skaman82/PowerPuck/PCB Files/Final Gerber/square Rev22_b.png

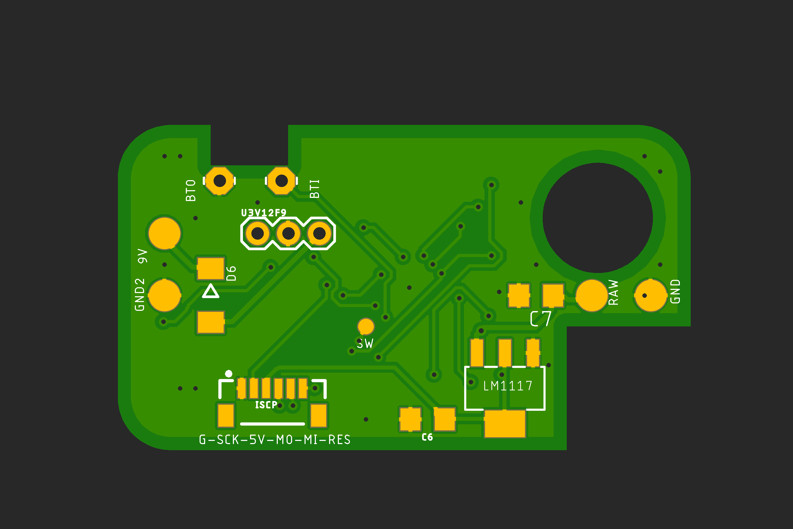
PCB Files/Final Gerber/square Rev22_b.png
